AdlerFarHorizons/ACS_ESP32/firmware/src/actuator.h

#include <ESP32Servo.h>
#include <analogWrite.h>
#include <ESP32Tone.h>
#include <ESP32PWM.h>

// Actuator
float currentActuatorExtension=50;
// int actuator_pin = 4;     //actuator Pin On Teensy 3.6
int actuator_pin = 17;       //actuator Pin On ESP32 DEVKIT V1
Servo actuator;              //create servo objects to control the linear actuator

void SetStrokePerc(float strokePercentage)
{
  if ( strokePercentage >= 1.0 && strokePercentage <= 99.0 )
  {
    int usec = 1000 + strokePercentage * ( 2000 - 1000 ) / 100.0 ;
    actuator.writeMicroseconds( usec );
  }
  currentActuatorExtension=strokePercentage;
}
